dotmote/sapflow/software/edge_compute_node/raspberry_pi/raspberry_pi.md

# Edge Compute with the Raspberry Pi

## Parts
- Raspberry Pi
- Raspberry Pi enclosure
- Raspberry Pi power supply
- MicroSD card (32+ GB ideally)
- WiFi Router

## Setup
1. Install/update [node + npm](https://thisdavej.com/upgrading-to-more-recent-versions-of-node-js-on-the-raspberry-pi/).
2. Install [mosquitto](https://randomnerdtutorials.com/how-to-install-mosquitto-broker-on-raspberry-pi/).
3. Download, install, and run the [MQTT broker script](/mqtt_nodejs).
4. Place the Raspberry Pi on the same WiFi network as the dataloggers.

## Considerations
- IP address
- setting up ntp sync
