dotmote/sapflow/software/microcontroller/d1_mini/d1.md

# D1 Mini Sapflow Firmware

## Setup
1. Follow Arduino-ESP8266 installation instructions here: https://github.com/esp8266/Arduino.
2. Install dependencies
3. Compile and upload to microcontroller

## Dependencies
- [ArduinoJSON](https://arduinojson.org/) by Benoit Blanchon
- [WiFi Manager](https://github.com/tzapu/WiFiManager) by Tzapu
- [PubSubClient](https://pubsubclient.knolleary.net/) by Nick O'Leary - NOTE: make sure to edit `PubSubClient.h` to increase its max packet size from 128 bytes to 512 bytes.
- [WEMOS SHT3x Arduino Library](https://github.com/wemos/WEMOS_SHT3x_Arduino_Library) (Optional - comment out applicable lines in firmware if unused)
- [HDC2080 Arduino Library](https://github.com/lime-labs/HDC2080-Arduino) by Lime Labs
