dotmote/sapflow/software/data_analysis/R/figs/gravi_climate_vpd.png

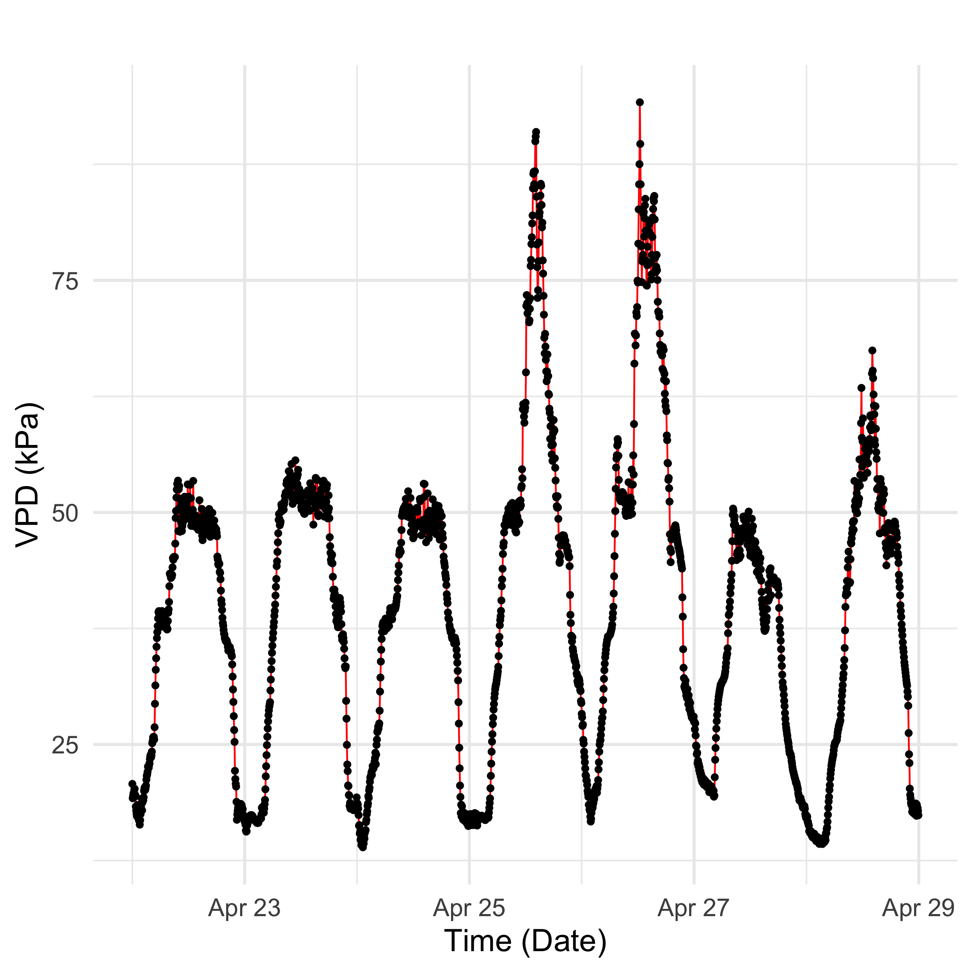
software/data_analysis/R/figs/gravi_climate_vpd.png
