dotmote/sapflow/software/data_analysis/R/figs/gravi_plot_25.png

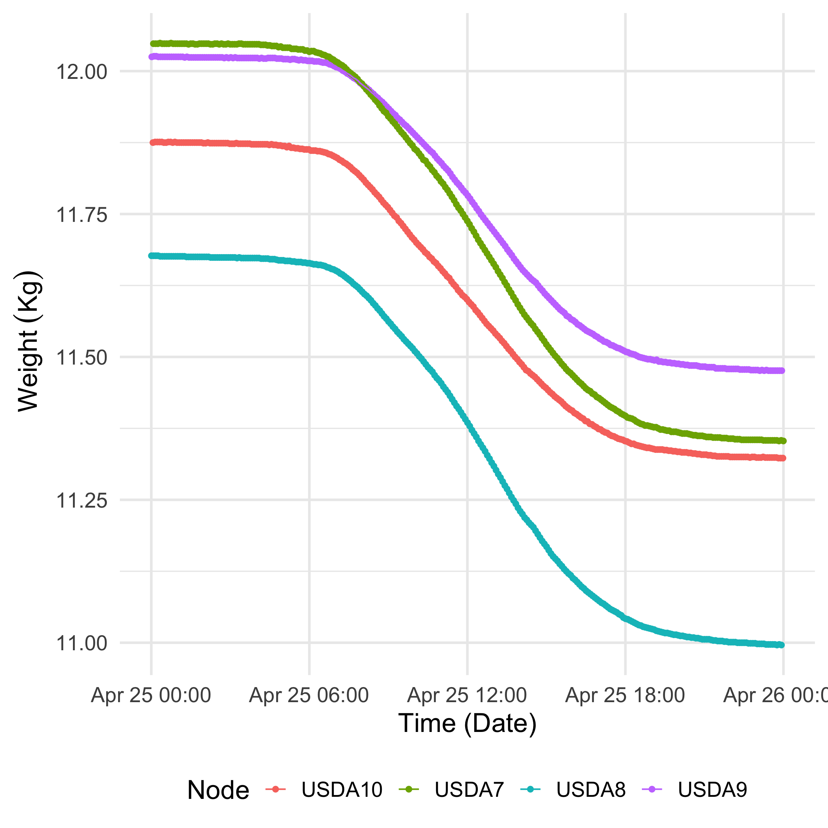
software/data_analysis/R/figs/gravi_plot_25.png
