dotmote/sapflow/software/data_analysis/R/figs/gravi_plot_28.png

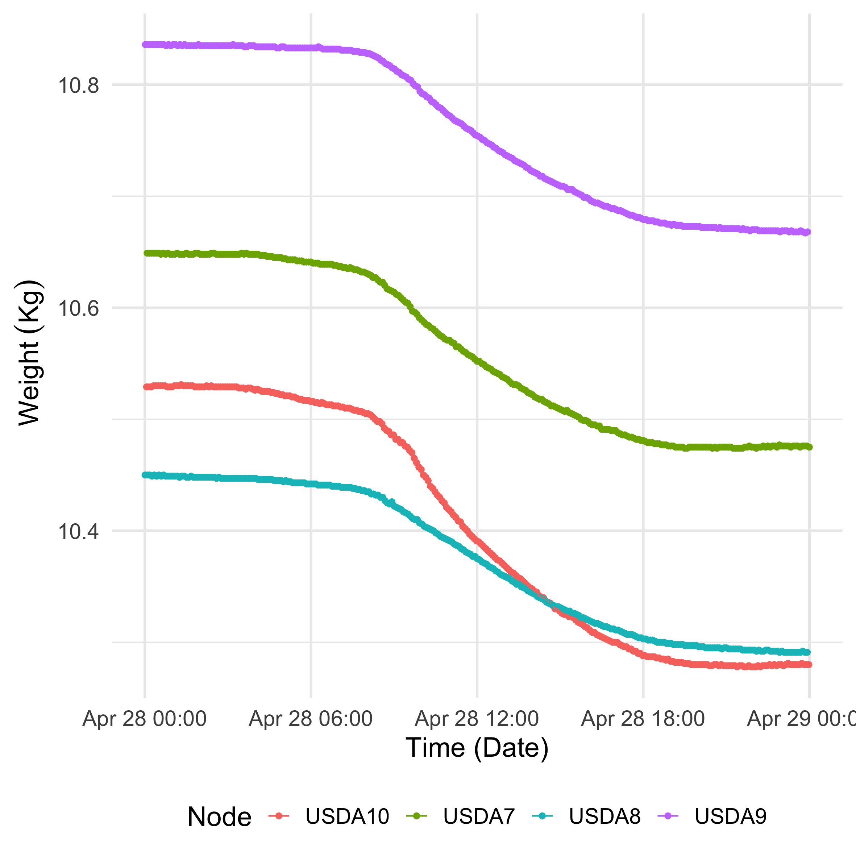
software/data_analysis/R/figs/gravi_plot_28.png
