dotmote/sapflow/software/data_analysis/R/figs/gravi_sapflow_timeseries_usda.png

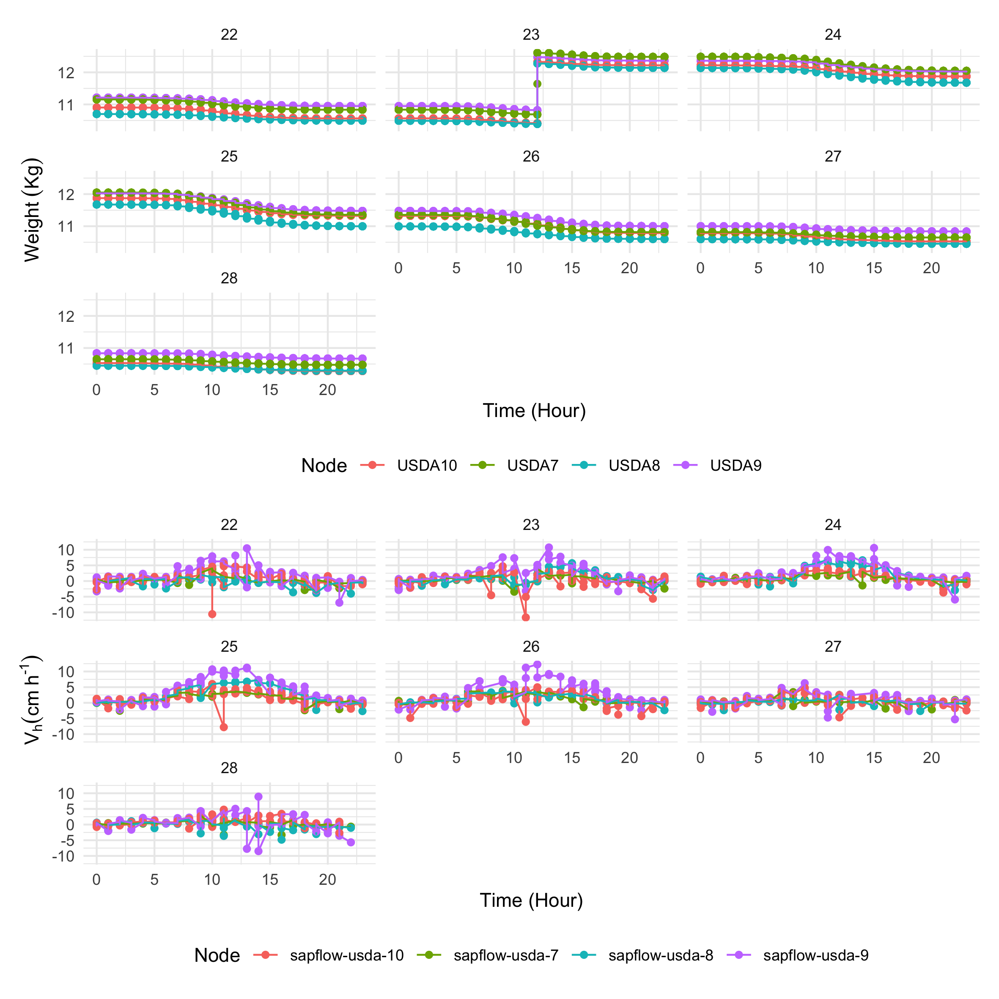
software/data_analysis/R/figs/gravi_sapflow_timeseries_usda.png
