dotmote/sapflow/software/data_analysis/R/figs/sap_gm_compare.png

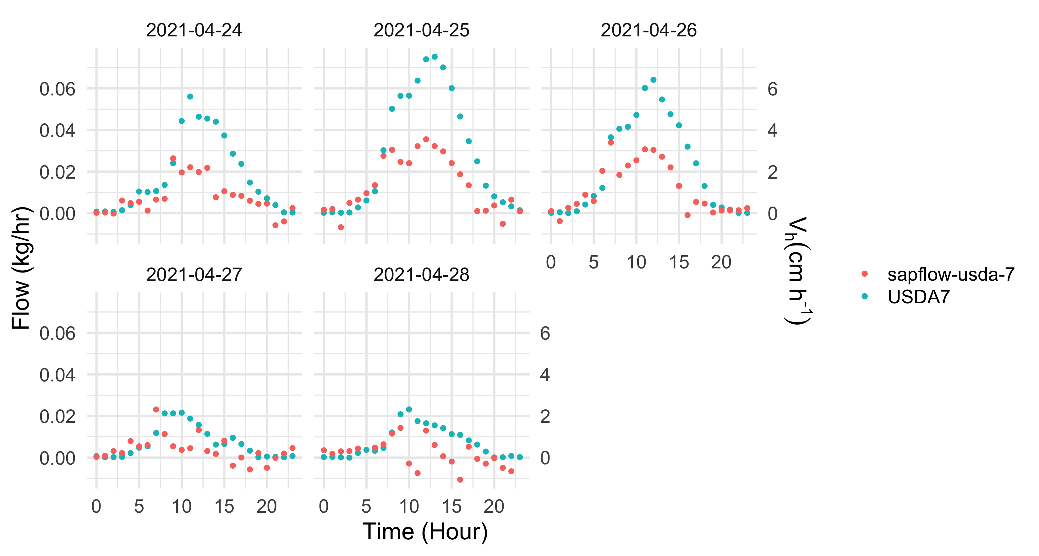
software/data_analysis/R/figs/sap_gm_compare.png
