dotmote/sapflow/software/data_analysis/R/figs/sap_gm_hourly_alldates.png

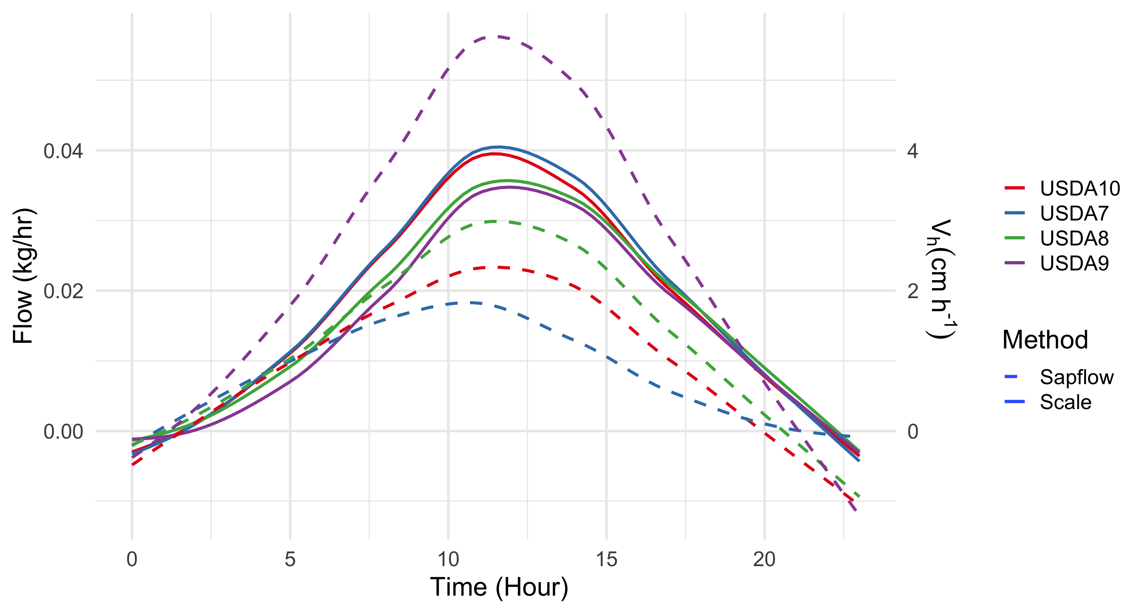
software/data_analysis/R/figs/sap_gm_hourly_alldates.png
