dotmote/sapflow/software/data_analysis/R/figs/sap_gm_hourly_alldates_seoff_day.png

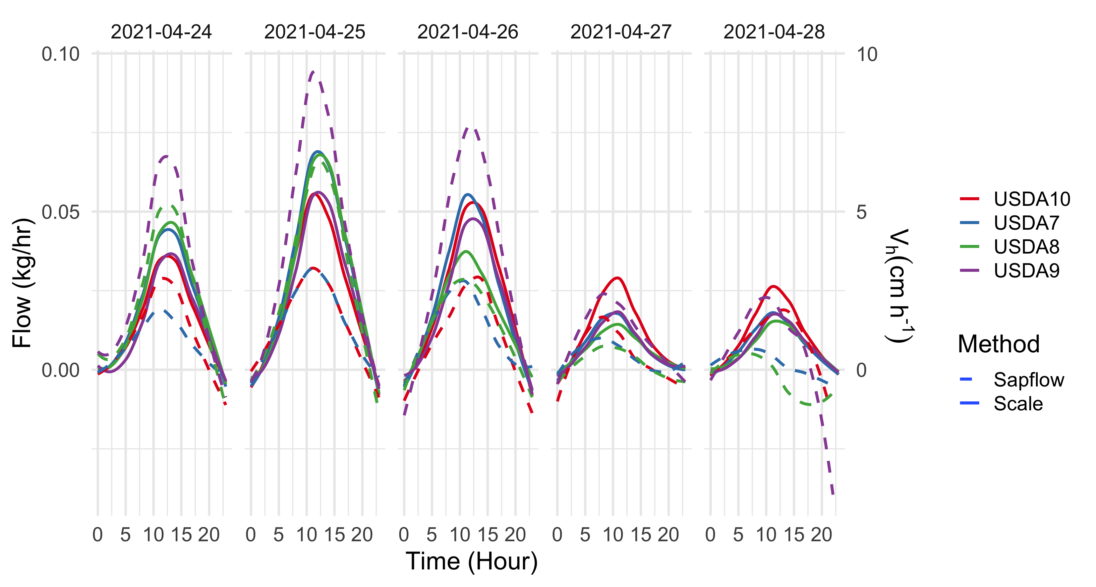
software/data_analysis/R/figs/sap_gm_hourly_alldates_seoff_day.png
