dotmote/sapflow/software/data_analysis/R/figs/sap_plot.png

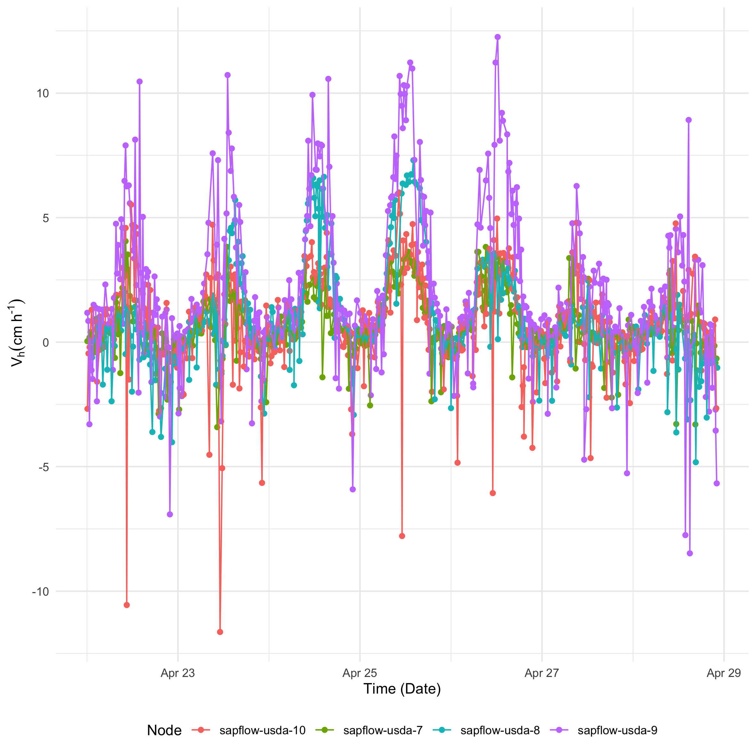
software/data_analysis/R/figs/sap_plot.png
