dotmote/sapflow/software/data_analysis/R/figs/sowit-stress-event.png

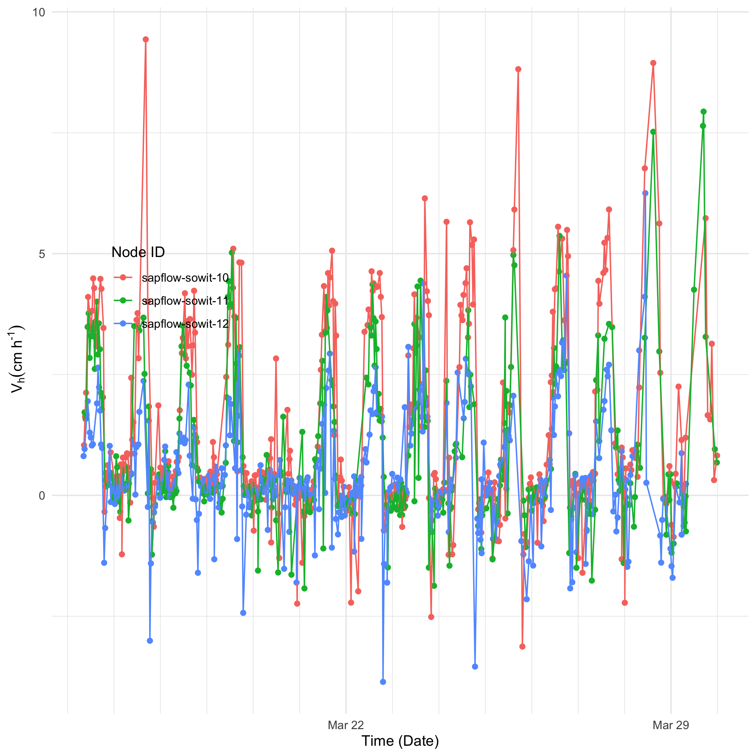
software/data_analysis/R/figs/sowit-stress-event.png
