dotmote/sapflow/software/data_analysis/R/figs/sowit-vh-smoothed.png

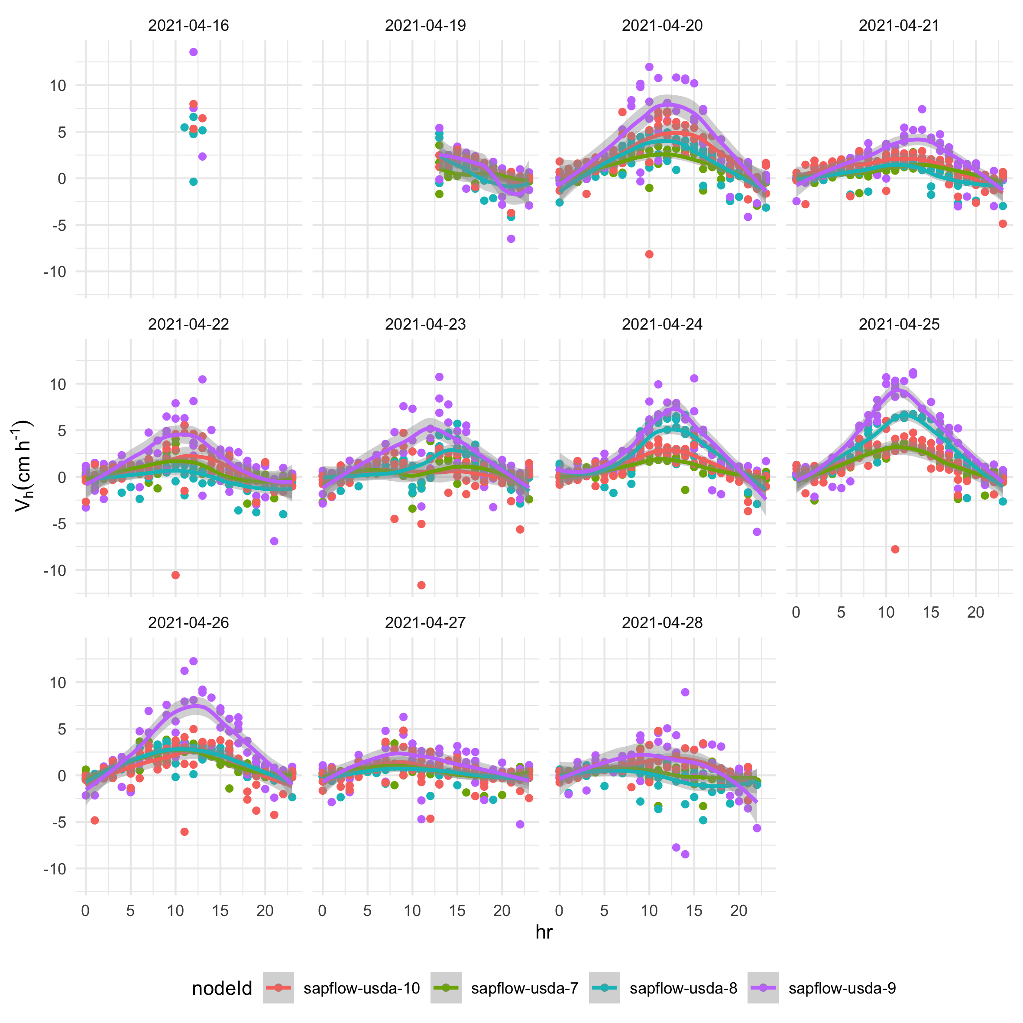
software/data_analysis/R/figs/sowit-vh-smoothed.png
