dotmote/sapflow/software/data_analysis/R/figs/stress-event.png

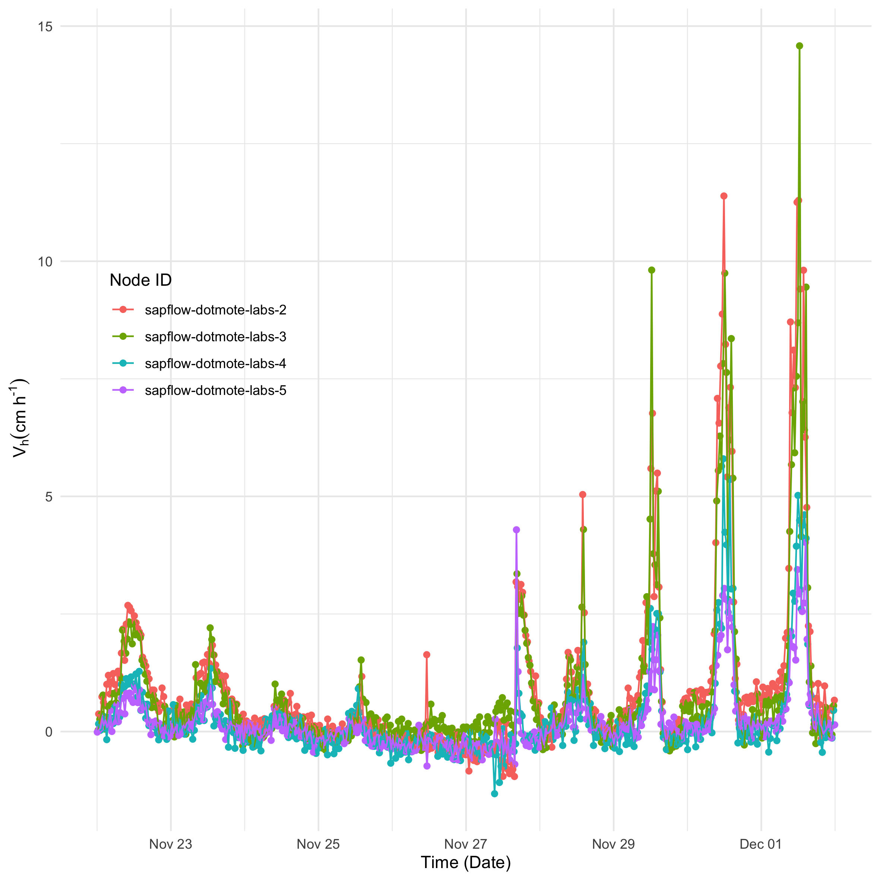
software/data_analysis/R/figs/stress-event.png
