dotmote/sapflow/software/data_analysis/R/figs/usda-graivimetric-Maize-stress-event.png

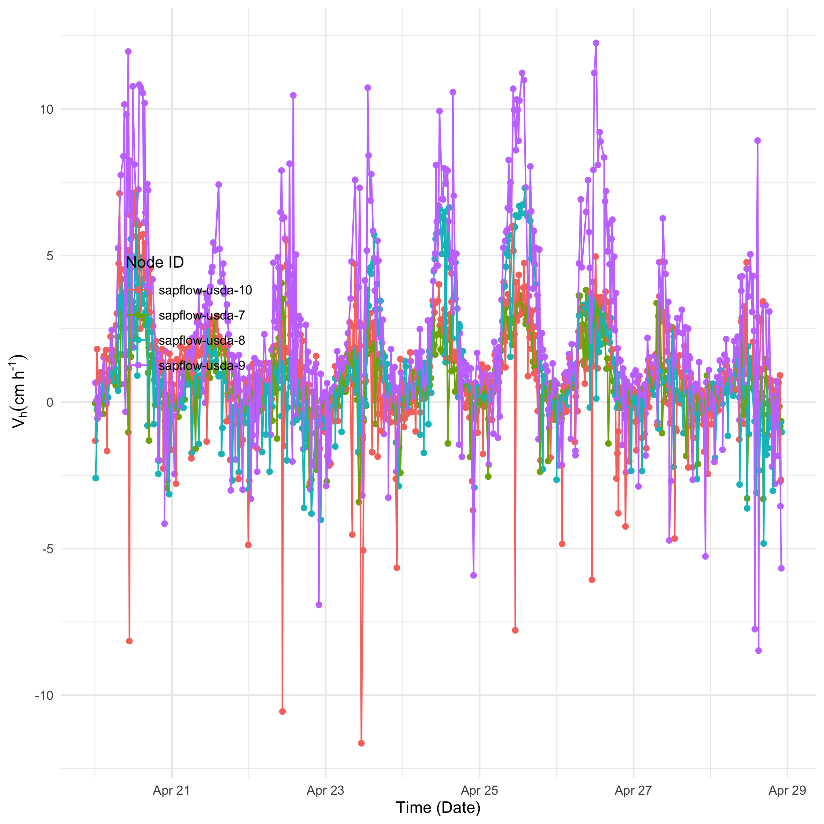
software/data_analysis/R/figs/usda-graivimetric-Maize-stress-event.png
